bcancinov/mdc-power-p16/sim/LT8350S.asc

@1: fra; delay=3m fstart=781.25 fend=200K oct=2 fcoarse=6.25K pp0=512m pp1=32m f0=781.25 f1=12.5K tavgmin=50µ tsettle=80µ
C1: cap; 15p
C2: cap; 10n
C3: cap; 1µ
C4: cap; 5.1p
C5: cap; 12.608µ; x4; Rser=2.172m Lser=0.2n
C6: cap; 22µ; Rser=40m Lser=1.7n
C7: cap; 100µ; Rser=80m Lser=3n
C8: cap; 20n
C10: cap; 12.608µ; Rser=2.172m Lser=0.2n
I1: current; PWL(0 0 4m 0 4.00001m 0.01 6m 0.01 6.0001m 0.1 8m 0.1 8.000001m 0.5)
R1: res; 100k
R2: res; 499k
R3: res; 80k
R4: res; 64.9k
R5: res; '16/0.5'
R6: res; 0.5
R7: res; 0.3
R8: res; '16/0.5'
RfbBot1: res; 7.32k
RfbTop1: res; 110k
Rfreq_1: res; 14.3k
U1: LT8350S
U2: XGL4020
U3: XGL4020
Vin1: voltage; 12
Named nets: 0, OUT, IN, ss, ldo
.tran 30m startup
If simulation model is not found, please "Sync release".
.fra startup
